gogogommez/Morse-Adapter/images/IMG_8195.jpeg

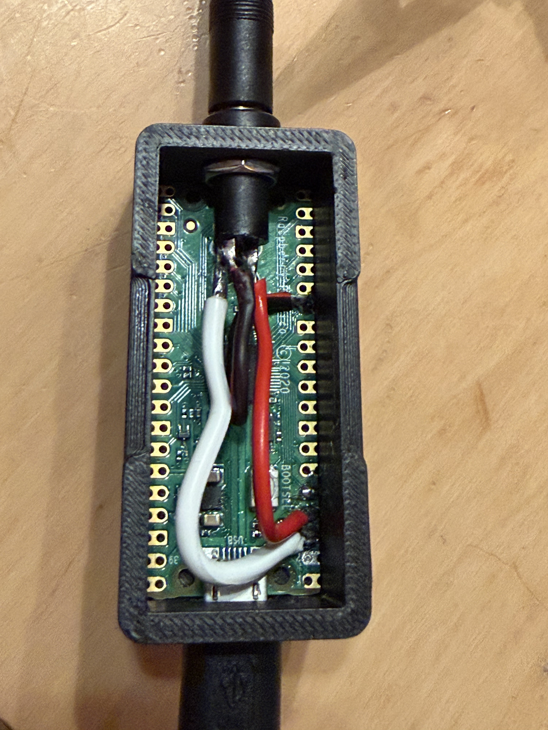
images/IMG_8195.jpeg
