gogogommez/Morse-Adapter/images/IMG_8209.jpeg

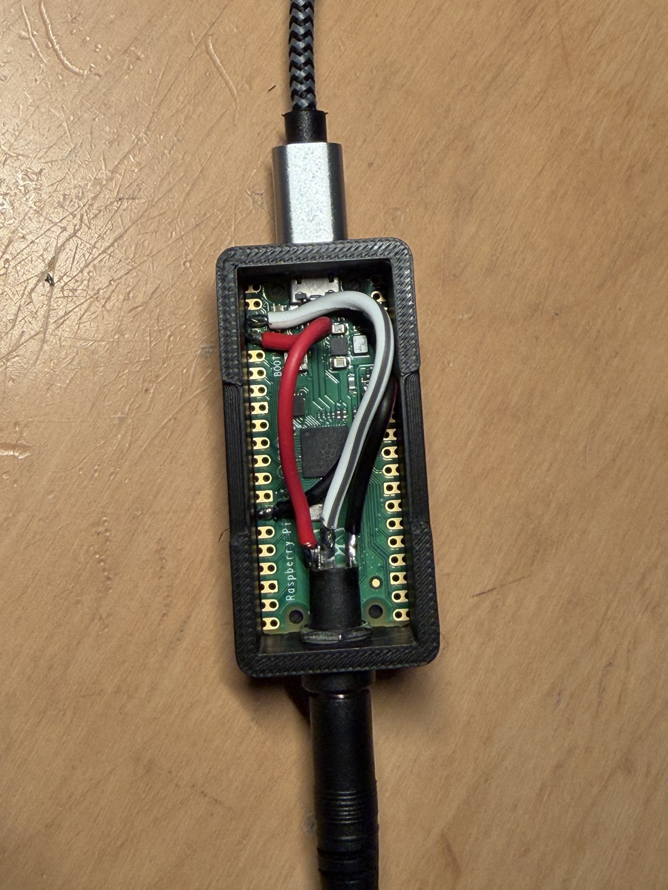
images/IMG_8209.jpeg
