gogogommez/Morse-Adapter/images/IMG_8215.jpeg

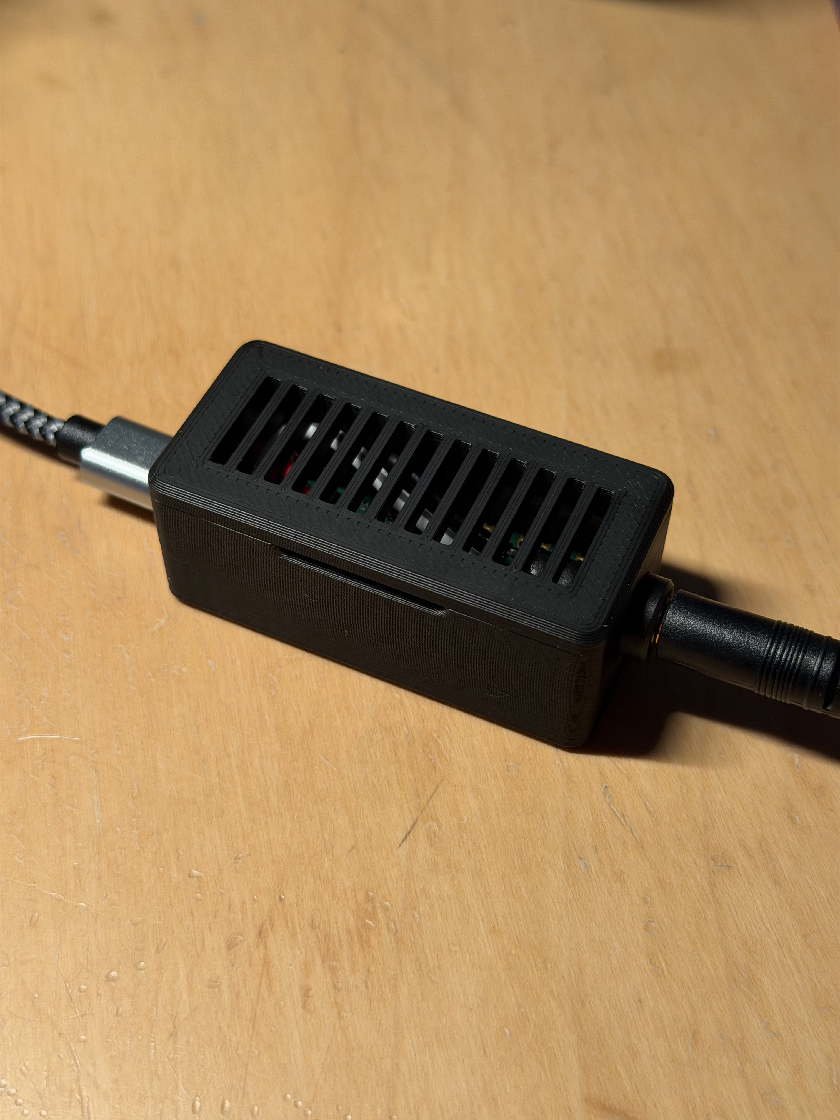
images/IMG_8215.jpeg
