gogogommez/Morse-Adapter/images/IMG_0271.jpeg

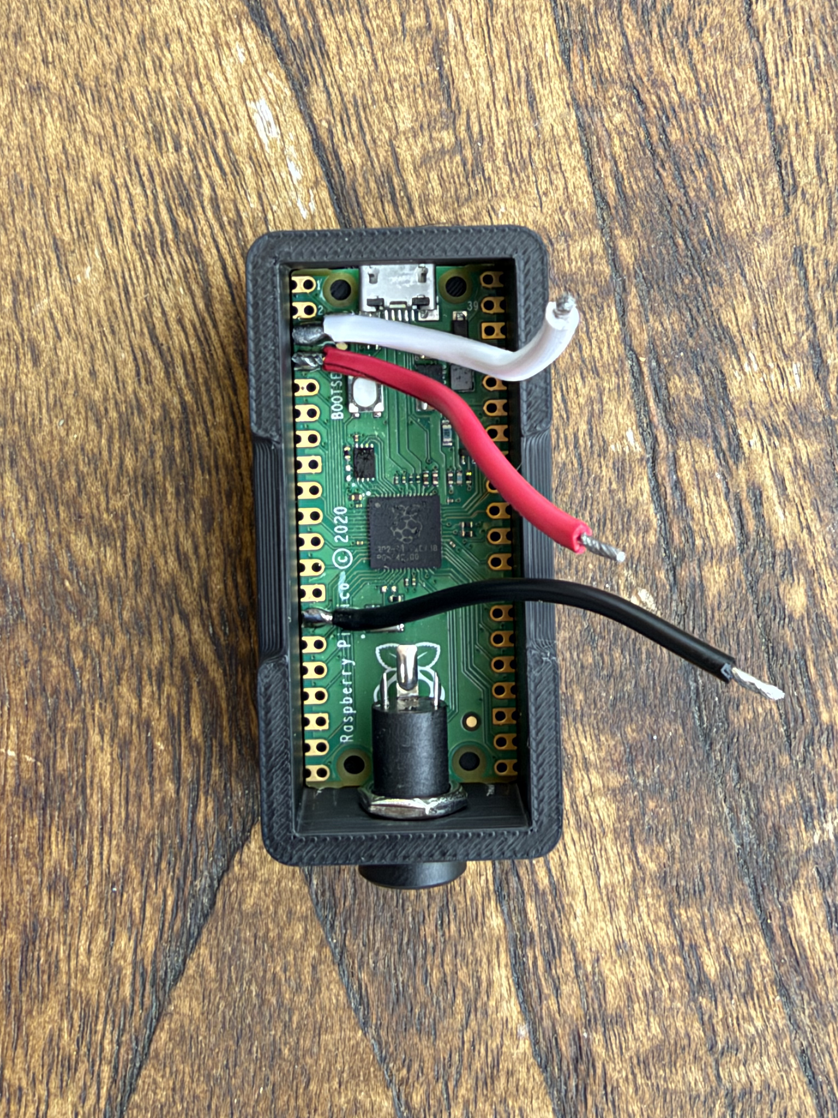
images/IMG_0271.jpeg
